romanecouedel/projetmsr_smart_glasses/Arduino/feuille_connexion.kicad_sch

## KiCad design Arduino/feuille_connexion.kicad_sch (2026-02-02)

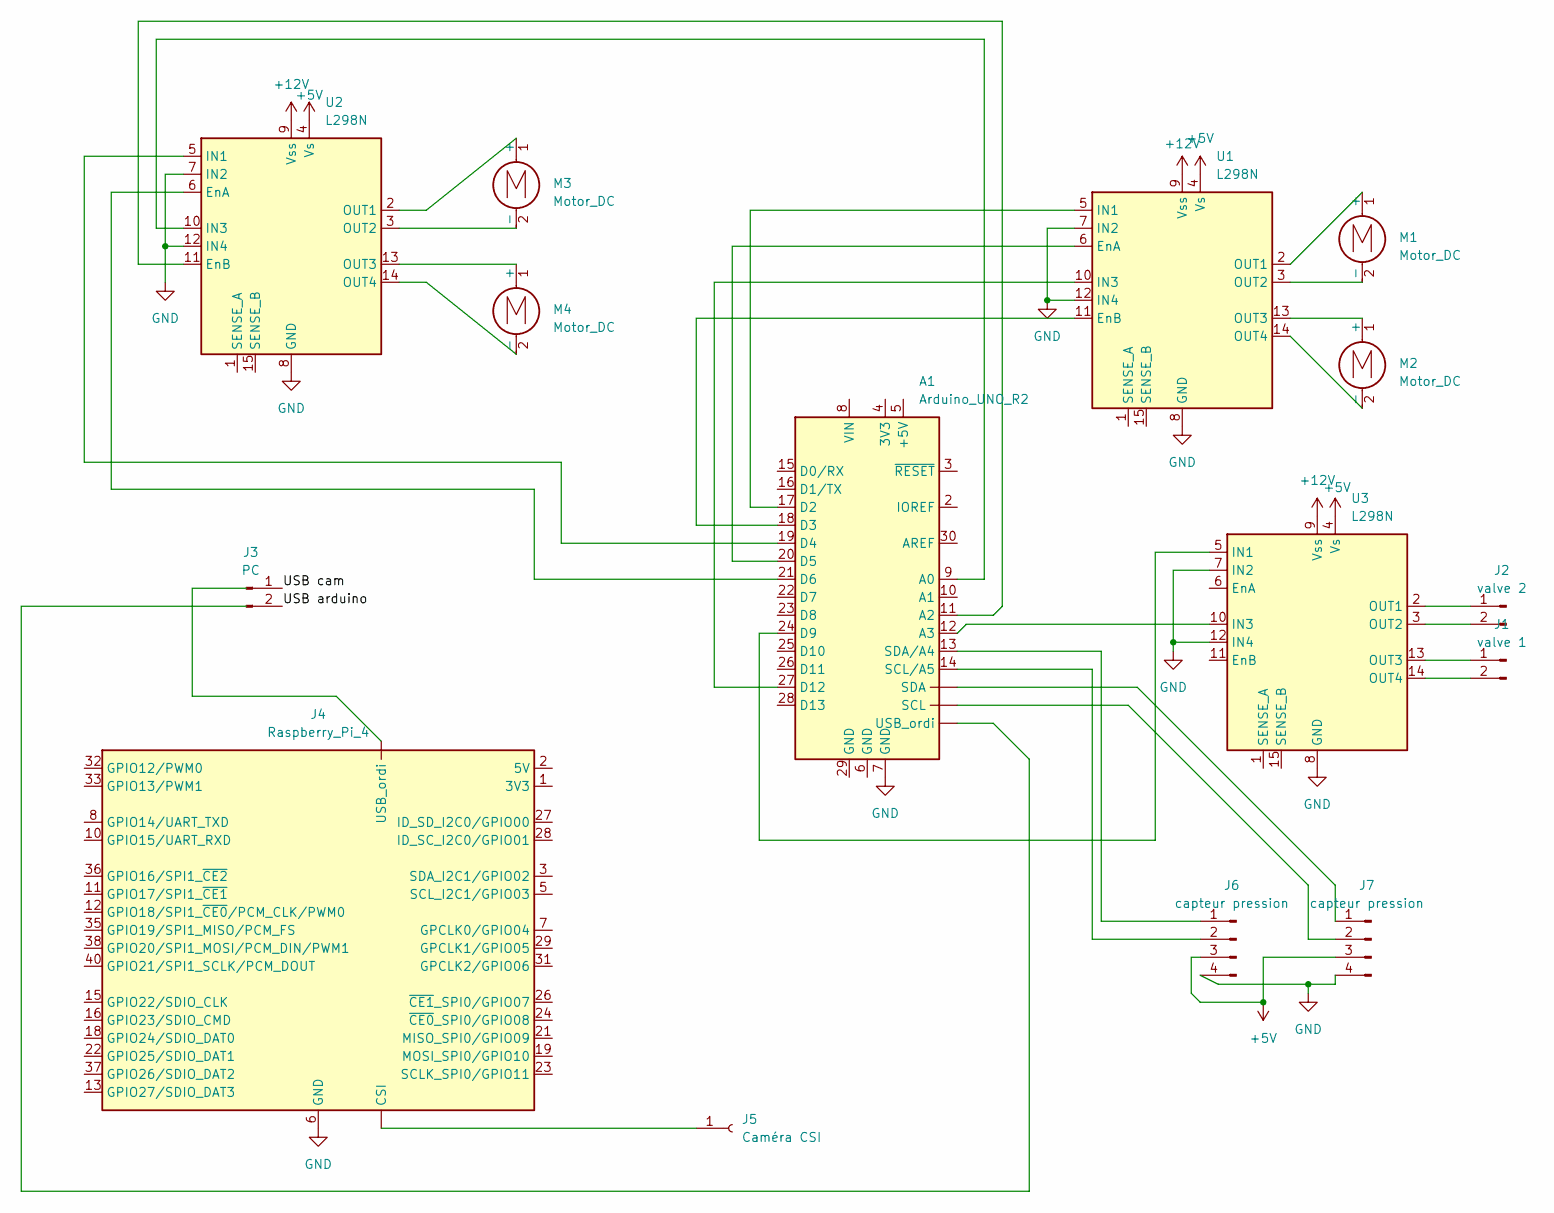
[picture p13: schematic feuille_connexion.kicad_sch]

Parts:
A1: Arduino_UNO_R2
J1: valve 1
J2: valve 2
J3: PC
J4: Raspberry_Pi_4
J5: Caméra CSI
J6, J7: capteur pression
M1, M2, M3, M4: Motor_DC
U1, U2, U3: L298N; TO-220-15_P2.54x5.08mm_StaggerOdd_Lead4.58mm_Vertical

Connections:
+5V: J6.3, J7.3, U1.4 (Vs), U2.4 (Vs), U3.4 (Vs)
+12V: U1.9 (Vss), U2.9 (Vss), U3.9 (Vss)
GND: A1.7 (GND), J4.6 (GND), J4.9 (GND), J4.14 (GND), J4.20 (GND), J4.25 (GND), J4.30 (GND), J4.34 (GND), J4.39 (GND), J6.4, J7.4, U1.7 (IN2), U1.8 (GND), U1.12 (IN4), U2.7 (IN2), U2.8 (GND), U2.12 (IN4), U3.7 (IN2), U3.8 (GND), U3.12 (IN4)
unnamed: A1.9 (A0), U2.10 (IN3)
unnamed: A1.11 (A2), U2.11 (EnB)
unnamed: A1.12 (A3), U3.10 (IN3)
unnamed: A1.13 (SDA/A4), J6.1
unnamed: A1.14 (SCL/A5), J6.2
unnamed: A1.17 (D2), U1.5 (IN1)
unnamed: A1.18 (D3), U1.11 (EnB)
unnamed: A1.19 (D4), U2.5 (IN1)
unnamed: A1.20 (D5), U1.6 (EnA)
unnamed: A1.21 (D6), U2.6 (EnA)
unnamed: A1.24 (D9), U3.5 (IN1)
unnamed: A1.27 (D12), U1.10 (IN3)
unnamed: A1. (SDA), J7.1, J7.2
unnamed: J1.1, U3.13 (OUT3)
unnamed: J1.2, U3.14 (OUT4)
unnamed: J2.1, U3.2 (OUT1)
unnamed: J2.2, U3.3 (OUT2)
unnamed: J4.1 (3V3), J4.17 (3V3)
unnamed: J4.2 (5V), J4.4 (5V)
unnamed: J4. (USB_ordi), J5.1
unnamed: M1.1 (+), U1.2 (OUT1)
unnamed: M1.2 (-), U1.3 (OUT2)
unnamed: M2.1 (+), U1.13 (OUT3)
unnamed: M2.2 (-), U1.14 (OUT4)
unnamed: M3.1 (+), U2.2 (OUT1)
unnamed: M3.2 (-), U2.3 (OUT2)
unnamed: M4.1 (+), U2.13 (OUT3)
unnamed: M4.2 (-), U2.14 (OUT4)
USB arduino: J3.2
USB cam: J3.1
